ssmo-oss/UMI-Power-distribution/archive/README.md

# Superseded designs — reference only

The original revC engineering-hold input and previously delivered D1–D5 snapshots are retained here for history. They are not current manufacturing instructions. Do not mix their BOMs, placement files or Gerbers with D6. Current editable designs are in `../design/D6`; current downloadable packages are in `../packages`.
