ssmo-oss/UMI-Power-distribution/design/D6S1/MAIN_POWER/review/MAIN_POWER.png

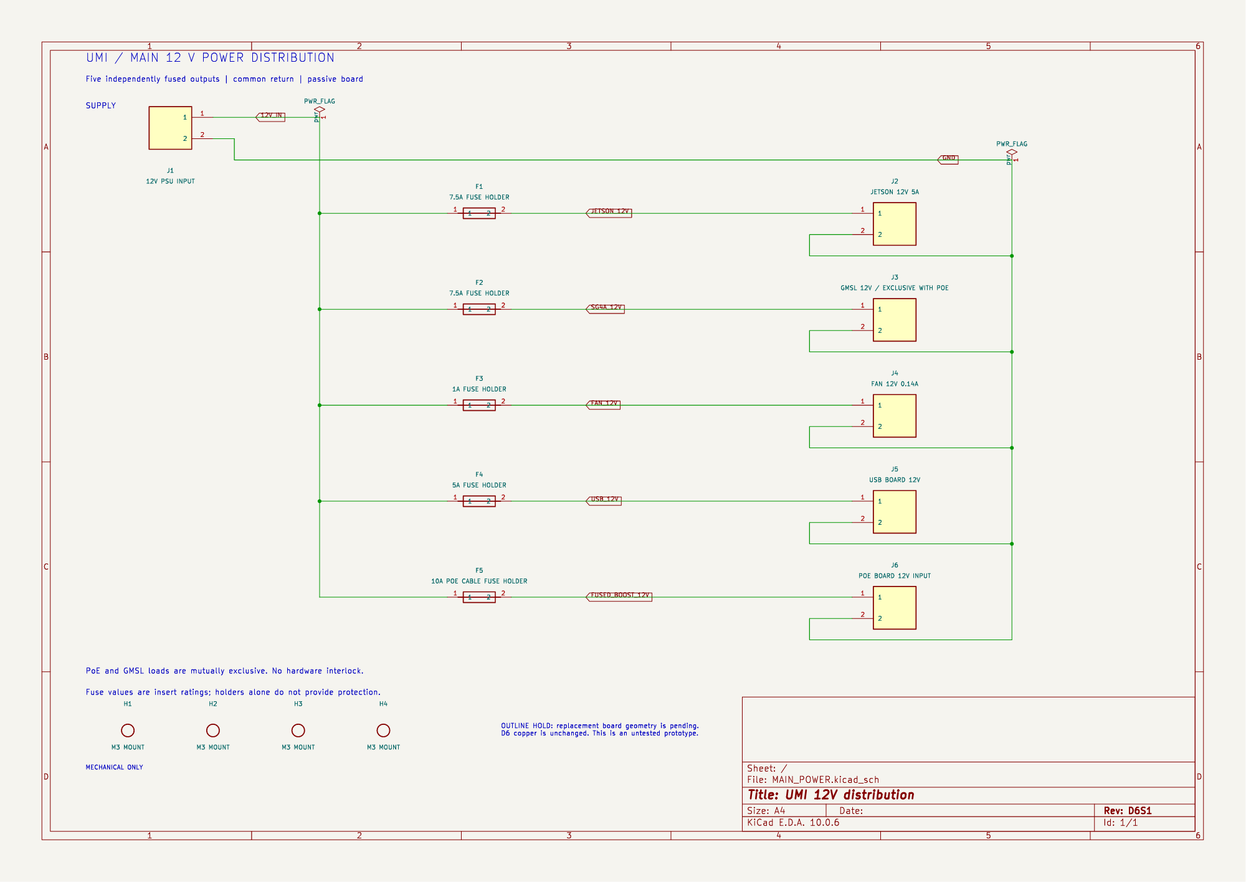
design/D6S1/MAIN_POWER/review/MAIN_POWER.png
