ssmo-oss/UMI-Power-distribution/design/D7-2L/MAIN_POWER/review/MAIN_POWER_top.png

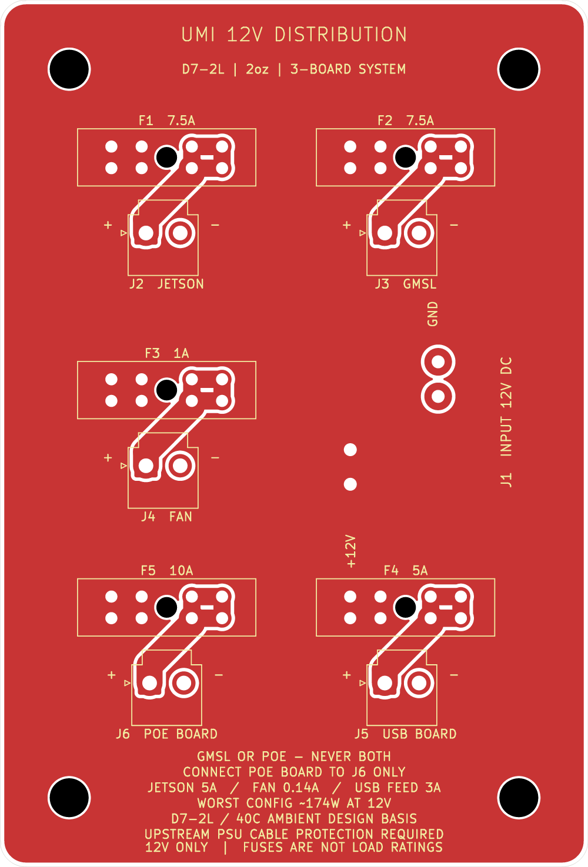
design/D7-2L/MAIN_POWER/review/MAIN_POWER_top.png
