ssmo-oss/UMI-Power-distribution/procurement/MAIN_D7_2L_UK_10/JLCPCB_CART.png

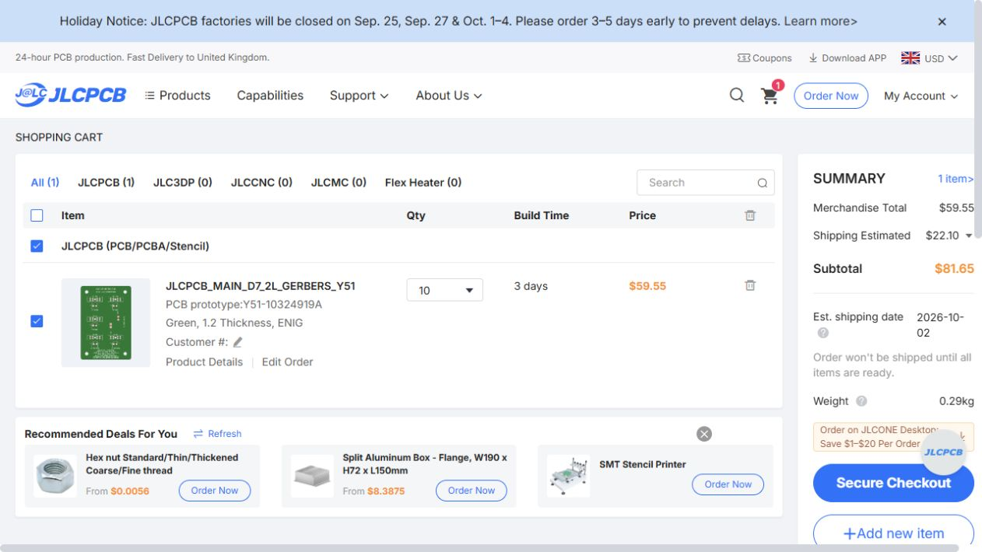
procurement/MAIN_D7_2L_UK_10/JLCPCB_CART.png
