ssmo-oss/UMI-Power-distribution/design/D6/POE_POWER/manufacturing/VIA_TREATMENT.csv

KiCad X mm | KiCad Y mm | Plot X mm | Plot Y mm | Hole mm | Treatment | UUID
80.04 | 49.5 | 16.04 | 60.5 | 0.4 | Epoxy filled and copper capped | 185ce832-b31d-5cbd-b1e6-7772da6d23e4
149.389 | 48.084 | 85.389 | 61.916 | 0.635 | Ordinary plated via; do not fill/cap | 3579963f-78b0-539c-87cf-163ce7b0c073
88.0 | 60.0 | 24.0 | 50.0 | 0.35 | Epoxy filled and copper capped | 36511814-321b-525e-9e22-42d1aa2e0944
129.330999 | 64.102002 | 65.330999 | 45.897998 | 0.254 | Epoxy filled and copper capped | 43bc7f10-7994-5b60-8514-b7c27d60b4fe
130.330999 | 65.102 | 66.330999 | 44.898 | 0.254 | Epoxy filled and copper capped | 45bfc4ca-efdd-530a-b04a-a414222d2000
77.96 | 49.5 | 13.96 | 60.5 | 0.4 | Epoxy filled and copper capped | 4919c850-3610-5eb3-ac36-f384cd702ceb
131.330999 | 64.102002 | 67.330999 | 45.897998 | 0.254 | Epoxy filled and copper capped | 4e2d5c46-ae0f-51cc-b3c1-d6e834f384e4
75.0 | 49.0 | 11.0 | 61.0 | 0.35 | Epoxy filled and copper capped | 5edb4d8f-2988-5751-b223-ea1b8ccd0565
76.25 | 60.2 | 12.25 | 49.8 | 0.35 | Epoxy filled and copper capped | 60e884db-ccdf-5e21-828e-16feece50997
152.564 | 48.084 | 88.564 | 61.916 | 0.635 | Ordinary plated via; do not fill/cap | 6312eecb-c30d-5e21-902c-9115aaf4c0aa
81.825 | 66.2 | 17.825 | 43.8 | 0.35 | Epoxy filled and copper capped | 643a4070-5fef-5e19-81c3-0a09f74bf5ea
129.330999 | 66.102001 | 65.330999 | 43.897999 | 0.254 | Epoxy filled and copper capped | 6629cf39-207b-5c1b-b85d-6aebcd45fa31
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
138.594 | 55.196 | 74.594 | 54.804 | 0.254 | Epoxy filled and copper capped | 5c8579ef-adf8-5500-81b3-074935e9211f
129.45 | 54.18 | 65.45 | 55.82 | 0.254 | Epoxy filled and copper capped | aa3be300-cc7f-588d-b817-2ce835791705
