ssmo-oss/UMI-Power-distribution/design/D6/USB_POWER/manufacturing/VIA_TREATMENT.csv

KiCad X mm | KiCad Y mm | Plot X mm | Plot Y mm | Hole mm | Treatment | UUID
42.85 | 35.2 | 32.85 | 24.8 | 0.3 | Epoxy filled and copper capped | 0c781a0a-a483-5db5-ad34-2bb7d4976b4d
25.3 | 30.9 | 15.3 | 29.1 | 0.3 | Epoxy filled and copper capped | 0e7574fd-eadc-5e98-8d1b-8e401af9450f
44.5 | 33.2 | 34.5 | 26.8 | 0.3 | Epoxy filled and copper capped | 1d2a9f01-7285-53b9-9de8-2bf83f6d7a26
32.875 | 32.0 | 22.875 | 28.0 | 0.3 | Epoxy filled and copper capped | 31a1aa65-a89b-554a-86f7-147ba5a9451c
25.3 | 30.2 | 15.3 | 29.8 | 0.3 | Epoxy filled and copper capped | 32226238-e256-5b39-b939-f04c4e5bf1d1
45.2 | 33.2 | 35.2 | 26.8 | 0.3 | Epoxy filled and copper capped | 34685283-3102-5a56-b6f6-d3f7f7a9b2a7
48.2 | 35.2 | 38.2 | 24.8 | 0.3 | Epoxy filled and copper capped | 35252cd1-7c23-5b58-ab69-cf94b8d3c861
42.375 | 25.0 | 32.375 | 35.0 | 0.3 | Epoxy filled and copper capped | 3d3ed0a9-b777-5aab-a963-b8690564f8b7
67.6 | 30.2 | 57.6 | 29.8 | 0.3 | Epoxy filled and copper capped | 3fa2a5a3-8100-5b1b-bb3b-c80359388c3a
48.85 | 35.9 | 38.85 | 24.1 | 0.3 | Epoxy filled and copper capped | 4710df1e-af6c-5049-b34d-b8f4752265ec
48.2 | 35.9 | 38.2 | 24.1 | 0.3 | Epoxy filled and copper capped | 52971339-0dc6-5303-8682-5041ea931b71
45.9 | 25.0 | 35.9 | 35.0 | 0.25 | Epoxy filled and copper capped | 743c5dca-5d07-554c-8f16-0c1da22238f5
67.6 | 30.9 | 57.6 | 29.1 | 0.3 | Epoxy filled and copper capped | 79289fc4-678c-5330-9882-e2661ff19181
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
27.1 | 16.4 | 17.1 | 43.6 | 0.3 | Epoxy filled and copper capped | a51179af-dbe3-54f5-b838-c7b29b098a20
27.8 | 16.4 | 17.8 | 43.6 | 0.3 | Epoxy filled and copper capped | cad131cc-2300-51fb-9e60-f965bdba593d
42.8 | 20.0 | 32.8 | 40.0 | 0.3 | Epoxy filled and copper capped | cc573699-fd69-5d87-876a-c7bf8403e0e7
53.1 | 20.0 | 43.1 | 40.0 | 0.3 | Epoxy filled and copper capped | f118ab5c-4baf-5383-8bab-6aa27422ec16
36.4 | 16.4 | 26.4 | 43.6 | 0.3 | Epoxy filled and copper capped | 165fc20b-54be-57b4-b76f-701978346e30
37.1 | 15.7 | 27.1 | 44.3 | 0.3 | Epoxy filled and copper capped | ad219f33-c5a7-587c-85aa-9fc9de97a235
37.1 | 16.4 | 27.1 | 43.6 | 0.3 | Epoxy filled and copper capped | e3531318-e589-52b4-9140-99bf0eac93a5
36.4 | 15.7 | 26.4 | 44.3 | 0.3 | Epoxy filled and copper capped | f0dc2eb6-da9e-5ec5-9f74-91d6365f5292
45.9 | 25.65 | 35.9 | 34.35 | 0.25 | Epoxy filled and copper capped | 5e713d4d-2d89-54bf-bc84-77916d6e6eea
51.85 | 24.35 | 41.85 | 35.65 | 0.3 | Epoxy filled and copper capped | 6fd73f04-96b9-54cf-af27-e370beb0d71f
